kmaximv/Wi-Fi-Sensor/screenshots/Apins.png

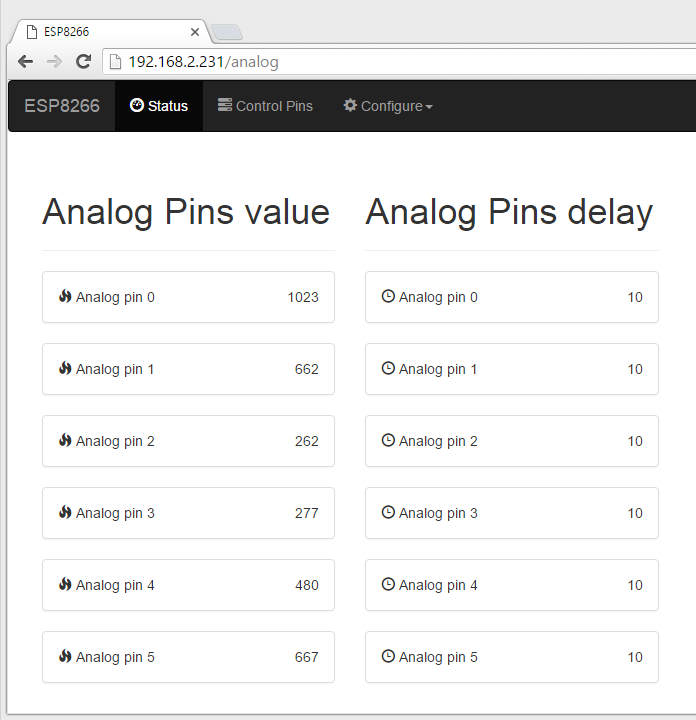
screenshots/Apins.png
