kmaximv/Wi-Fi-Sensor/screenshots/arduino-ide.png

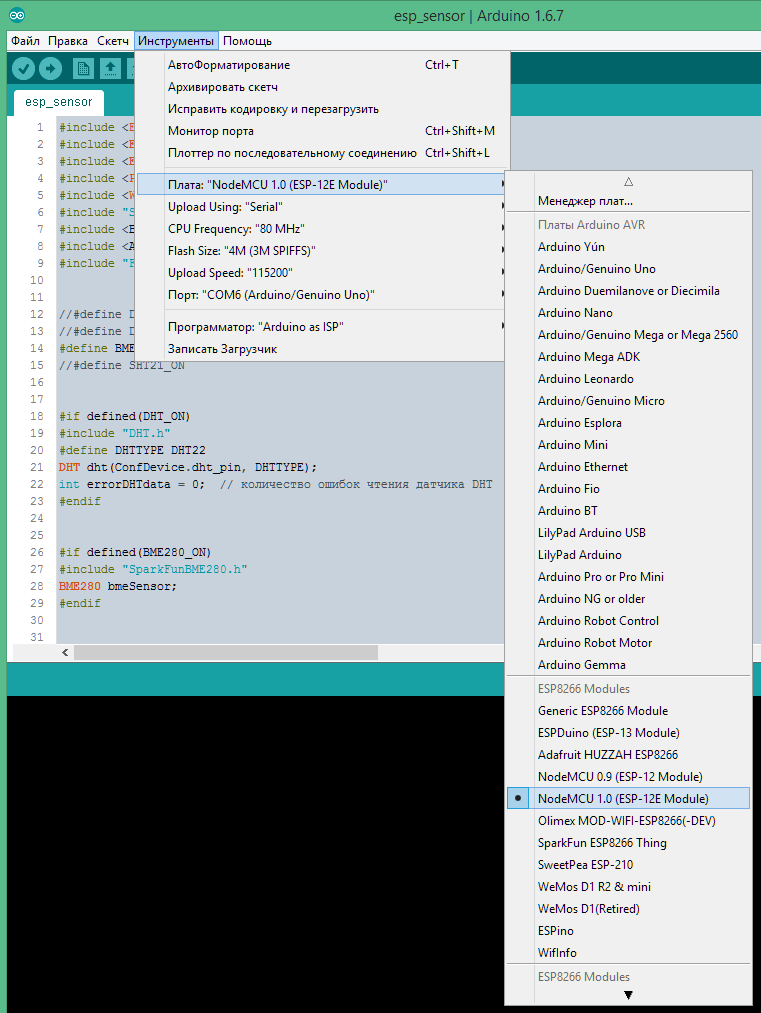
screenshots/arduino-ide.png
