kmaximv/Wi-Fi-Sensor/screenshots/HC-SR501.jpg

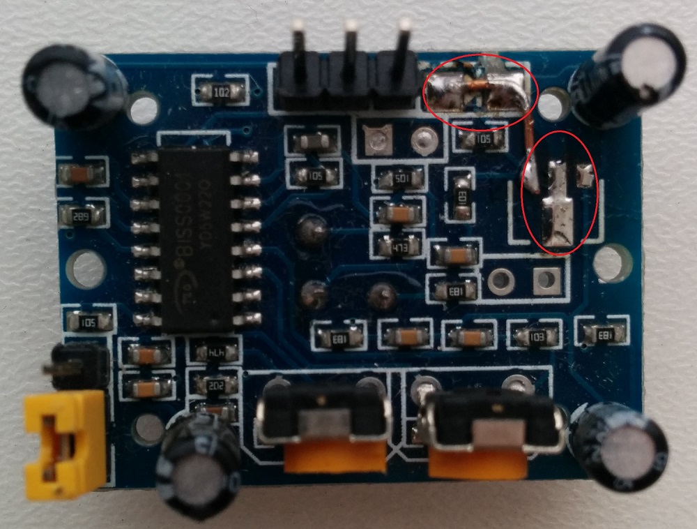
screenshots/HC-SR501.jpg
