kmaximv/Wi-Fi-Sensor/screenshots/MP1584EN.jpg

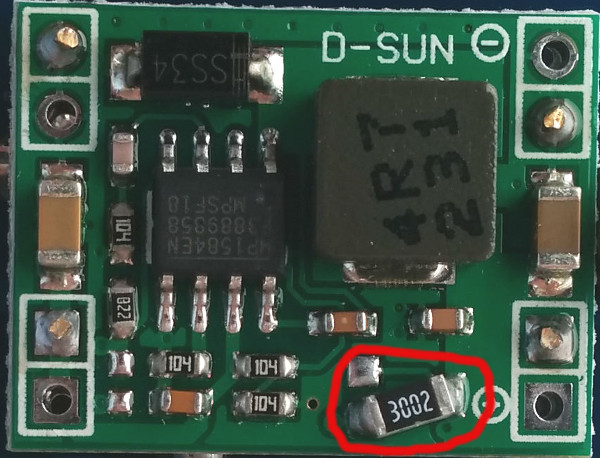
screenshots/MP1584EN.jpg
