kmaximv/Wi-Fi-Sensor/screenshots/OpenHab_graph.png

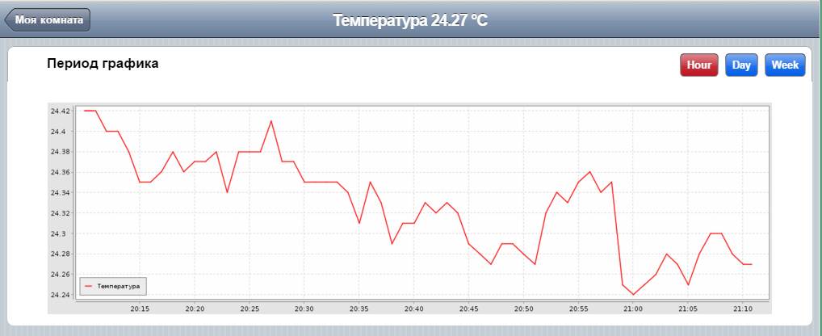
screenshots/OpenHab_graph.png
