kmaximv/Wi-Fi-Sensor/screenshots/PCB_top.png

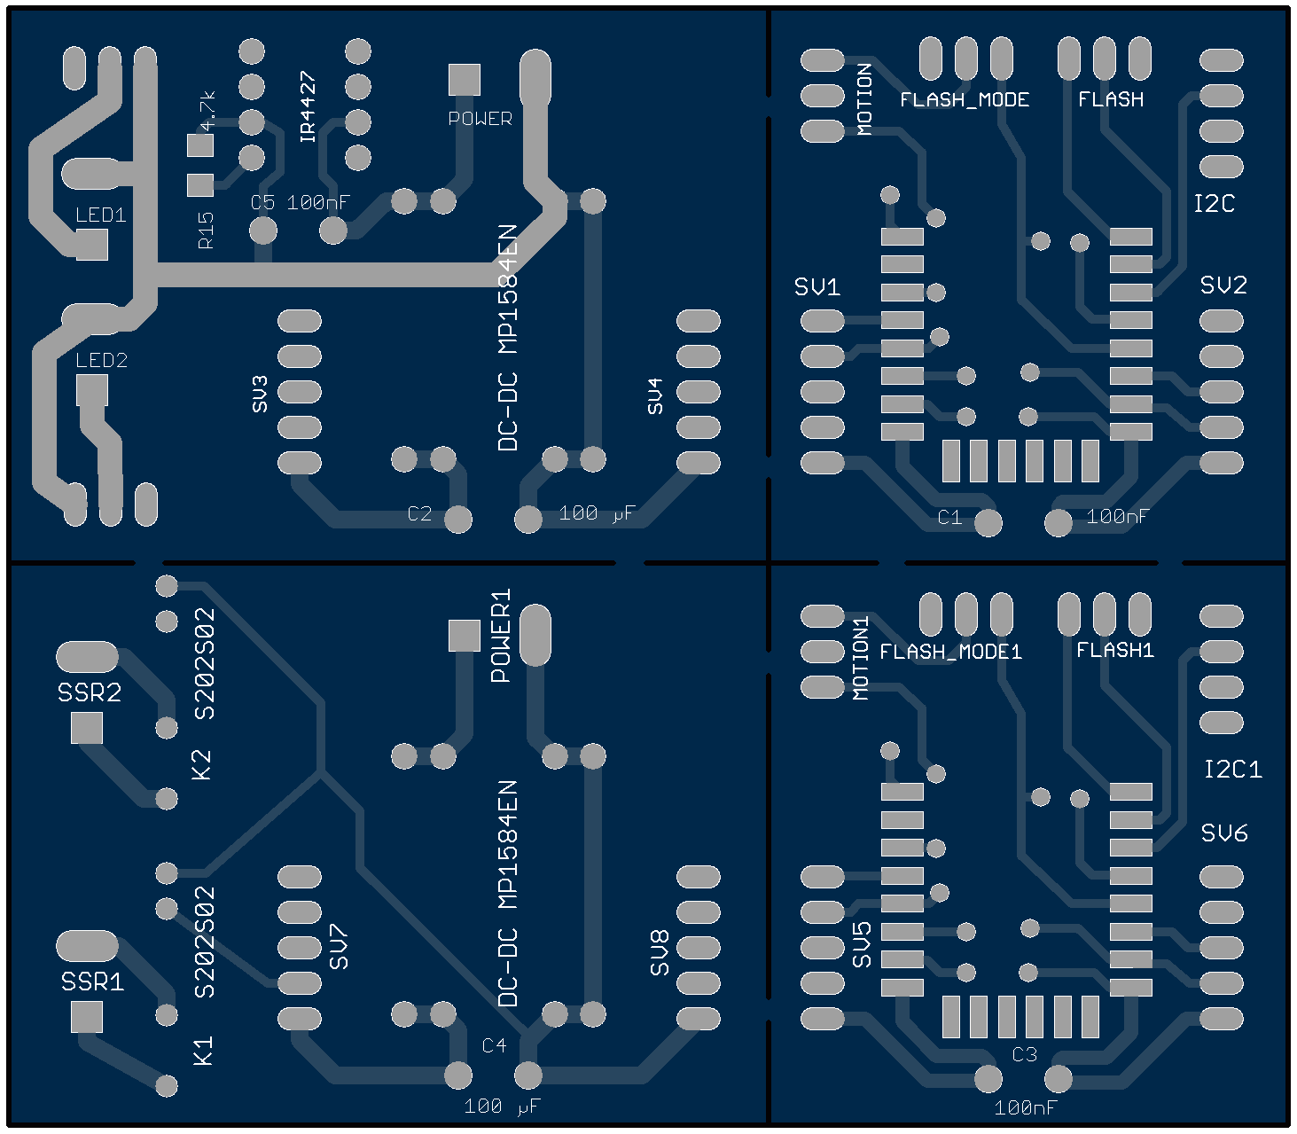
screenshots/PCB_top.png
