kmaximv/Wi-Fi-Sensor/screenshots/PZEM/CuteCom.png

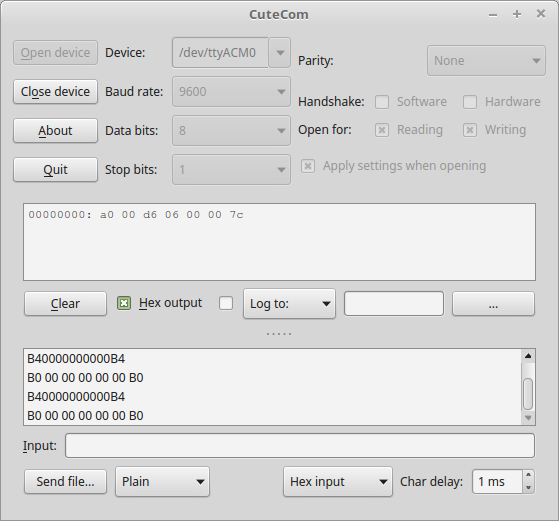
screenshots/PZEM/CuteCom.png
