kmaximv/Wi-Fi-Sensor/screenshots/PZEM/OpenHab_energy.png

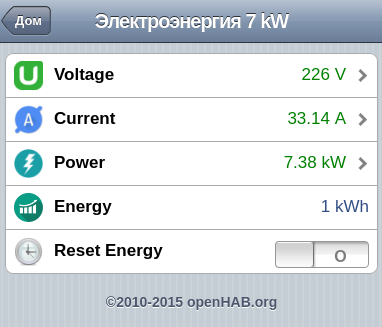
screenshots/PZEM/OpenHab_energy.png
