kmaximv/Wi-Fi-Sensor/screenshots/PZEM/pzem_status.png

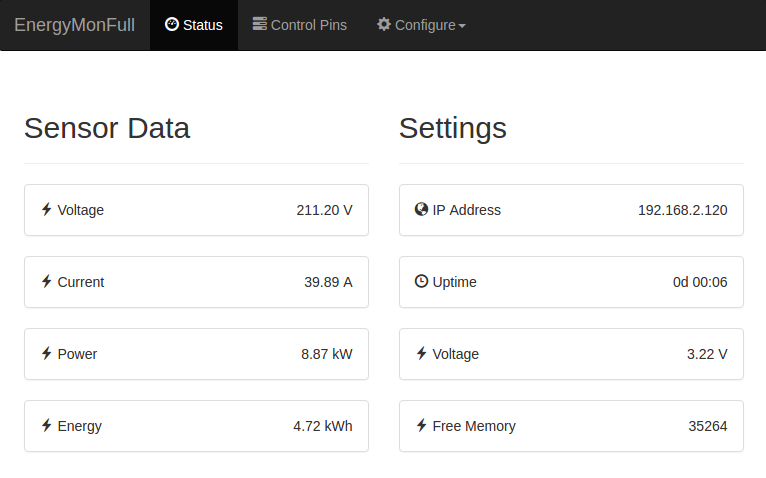
screenshots/PZEM/pzem_status.png
