kmaximv/Wi-Fi-Sensor/screenshots/Schema_LED.png

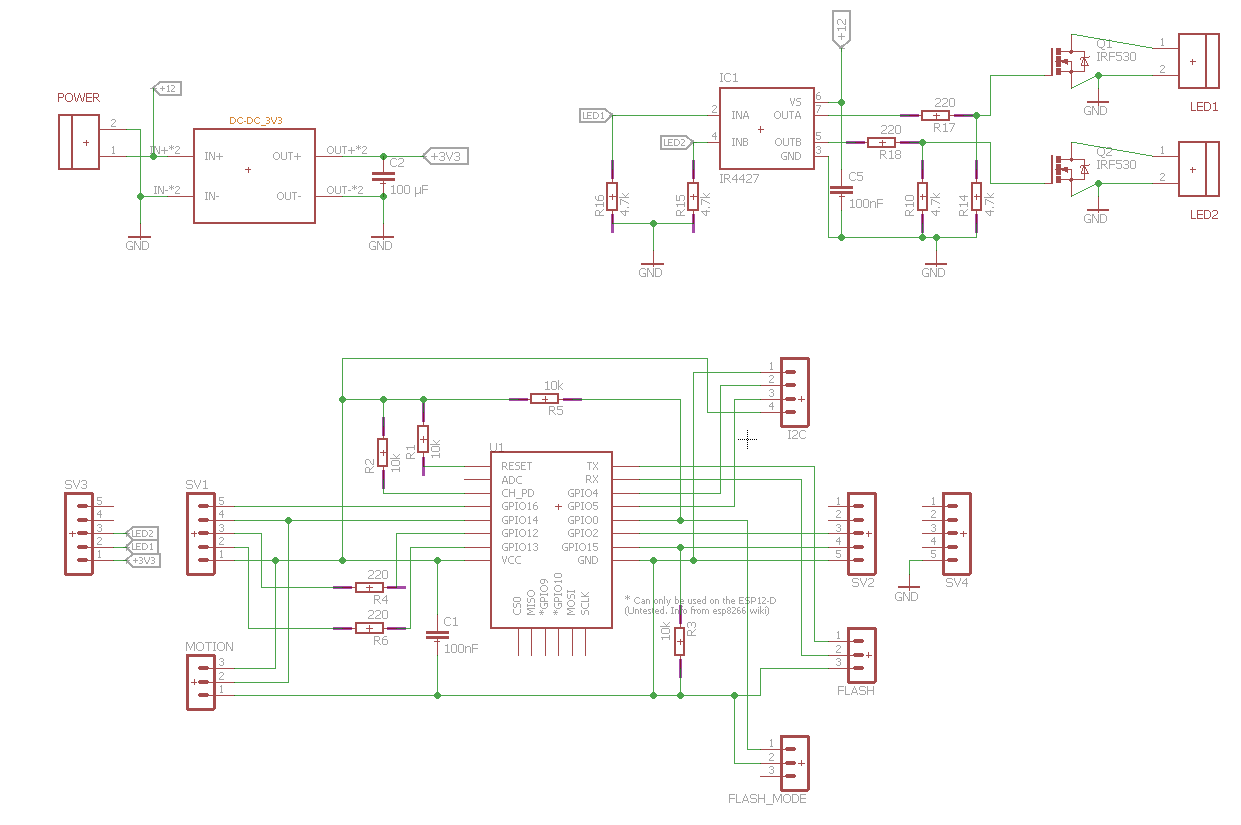
screenshots/Schema_LED.png
