kmaximv/Wi-Fi-Sensor/screenshots/Schema_SSR.png

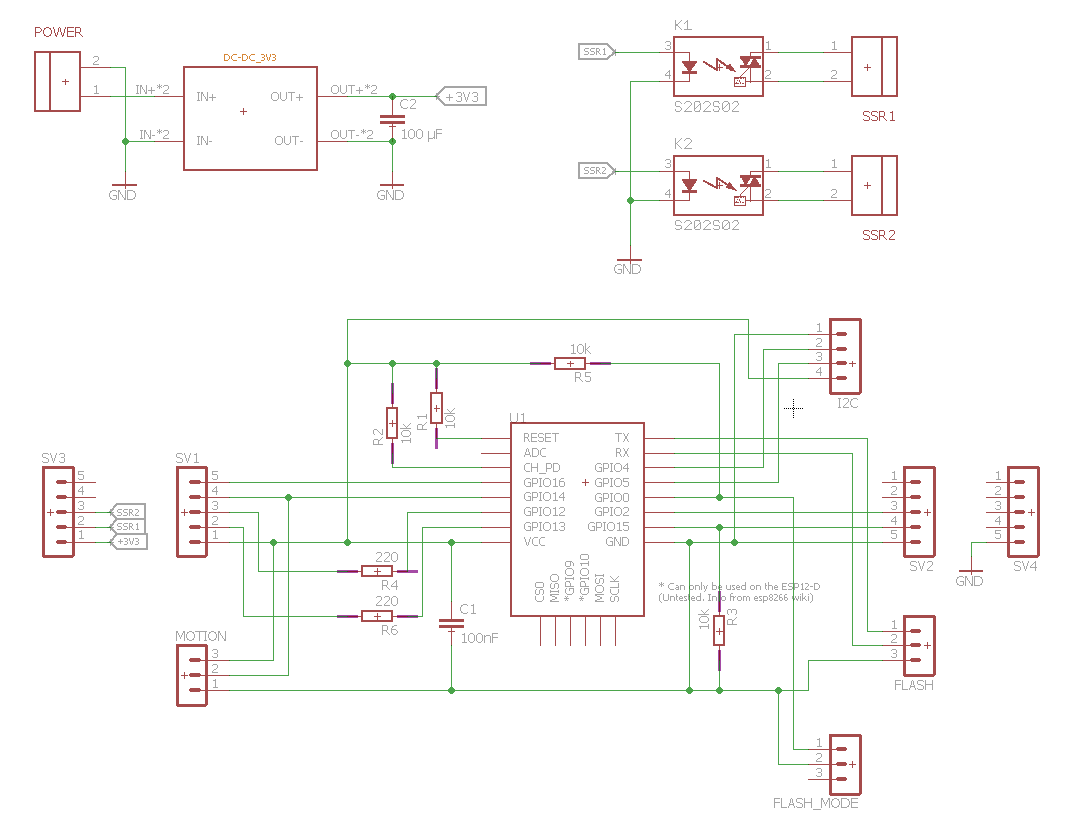
screenshots/Schema_SSR.png
