kmaximv/Wi-Fi-Sensor/screenshots/syslog.png

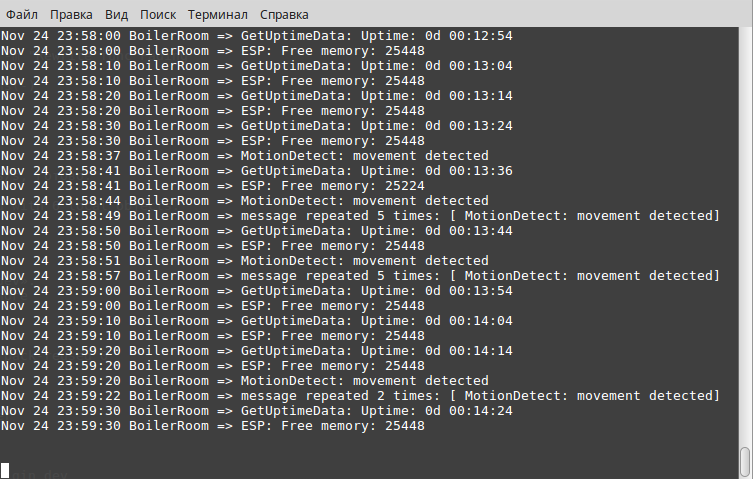
screenshots/syslog.png
