kmaximv/Wi-Fi-Sensor/screenshots/thumbs/PCB_top_th.png

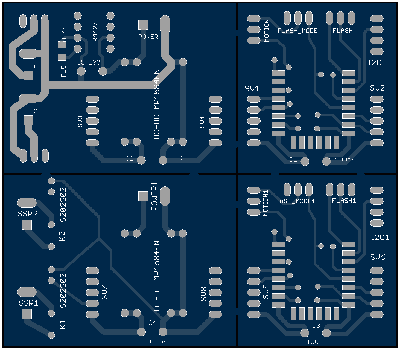
screenshots/thumbs/PCB_top_th.png
