kmaximv/Wi-Fi-Sensor/screenshots/web/console.png

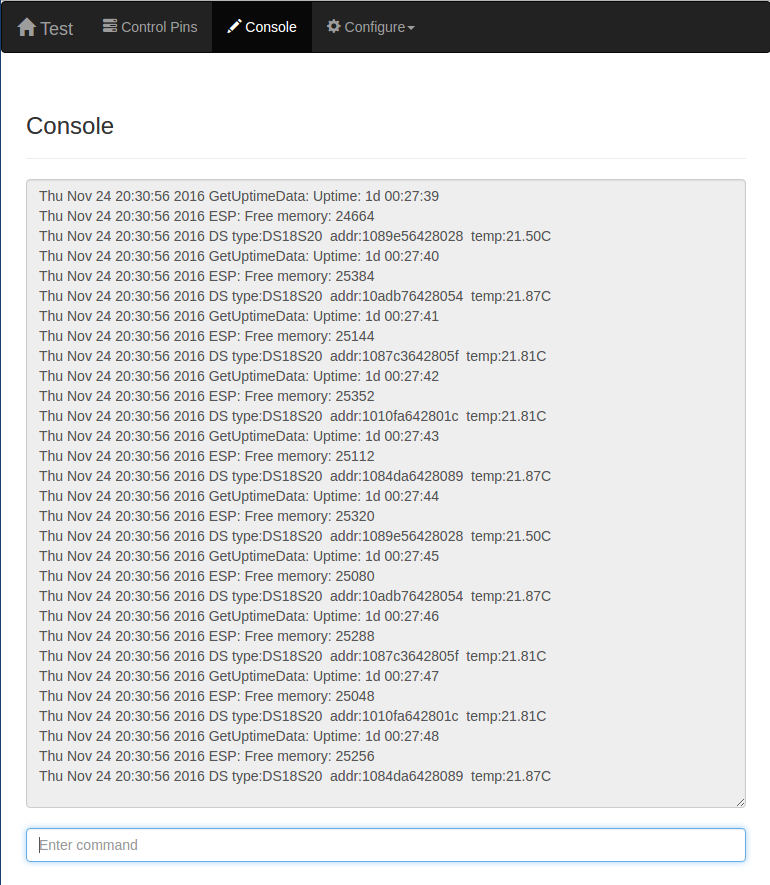
screenshots/web/console.png
