kmaximv/Wi-Fi-Sensor/screenshots/web/control.png

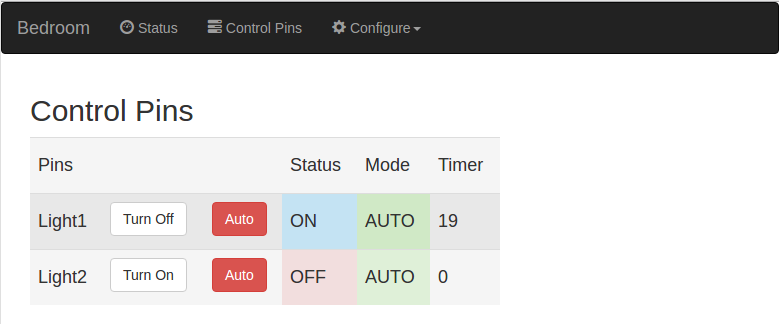
screenshots/web/control.png
