kmaximv/Wi-Fi-Sensor/screenshots/web/esp.png

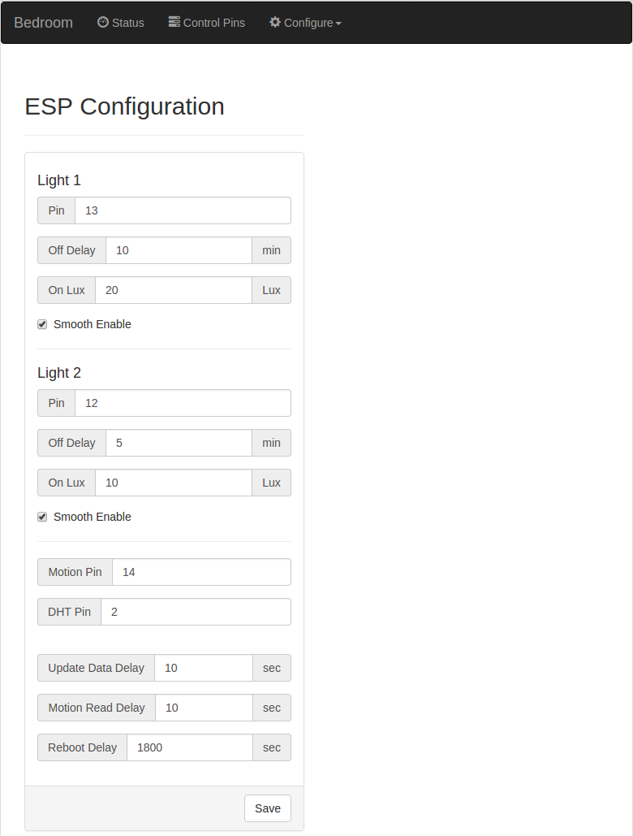
screenshots/web/esp.png
