kmaximv/Wi-Fi-Sensor/screenshots/web/logConf.png

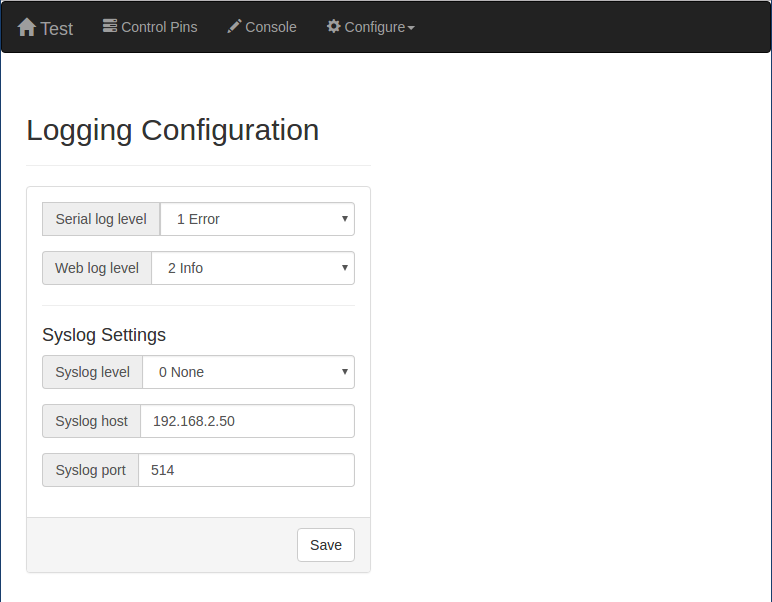
screenshots/web/logConf.png
