kmaximv/Wi-Fi-Sensor/screenshots/web/menu.png

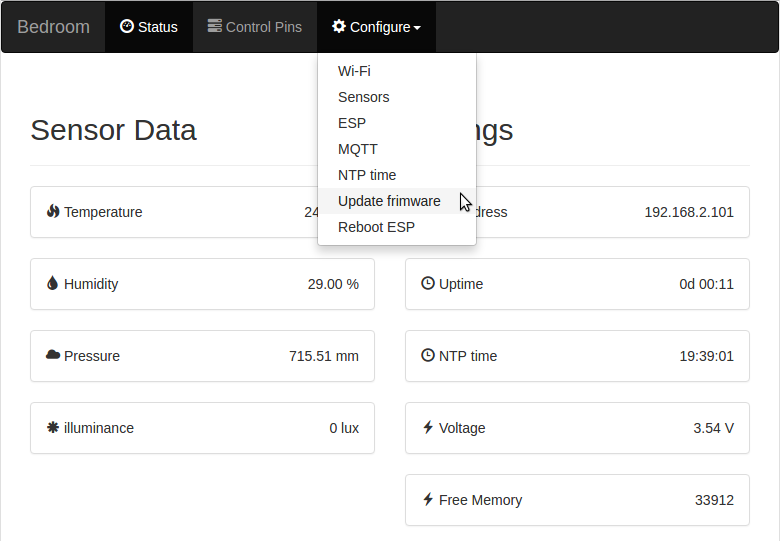
screenshots/web/menu.png
