kmaximv/Wi-Fi-Sensor/screenshots/web/mqtt.png

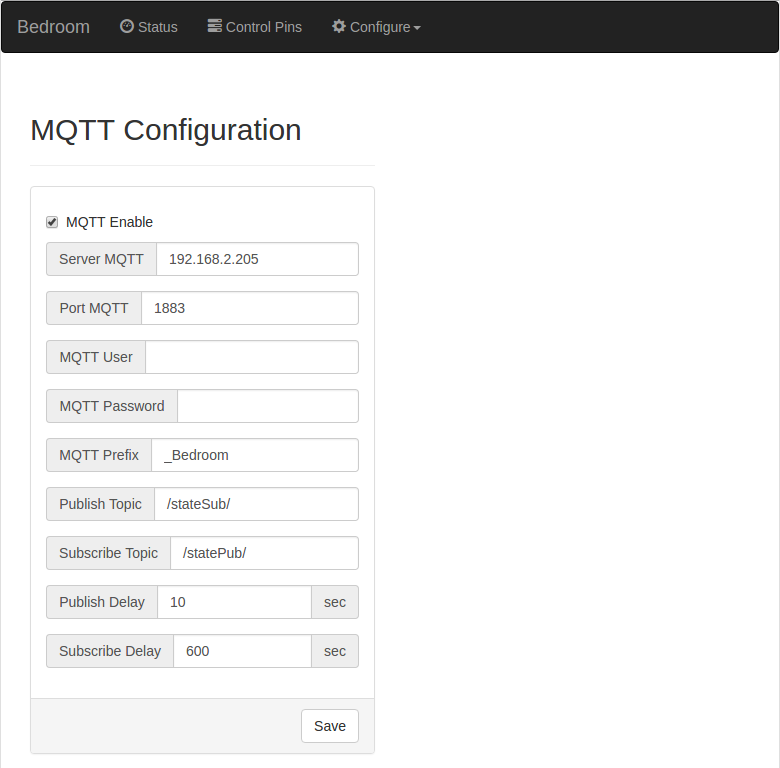
screenshots/web/mqtt.png
