kmaximv/Wi-Fi-Sensor/screenshots/web/ntp.png

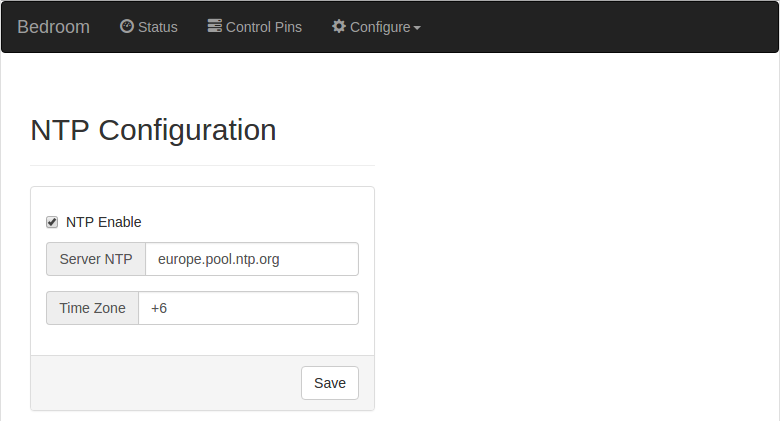
screenshots/web/ntp.png
