kmaximv/Wi-Fi-Sensor/screenshots/web/sensors.png

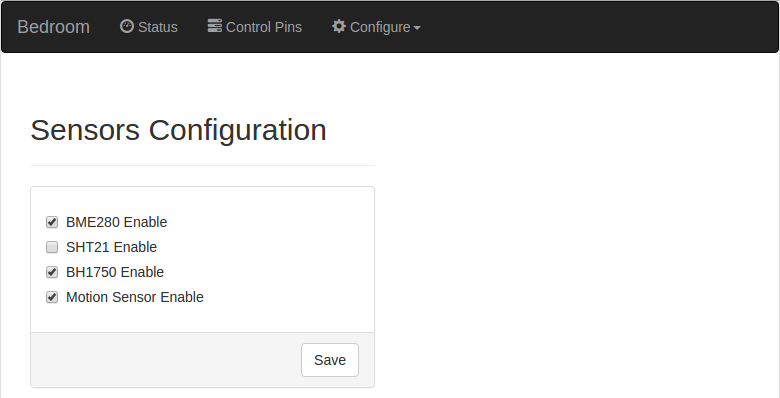
screenshots/web/sensors.png
