kmaximv/Wi-Fi-Sensor/screenshots/web/status.png

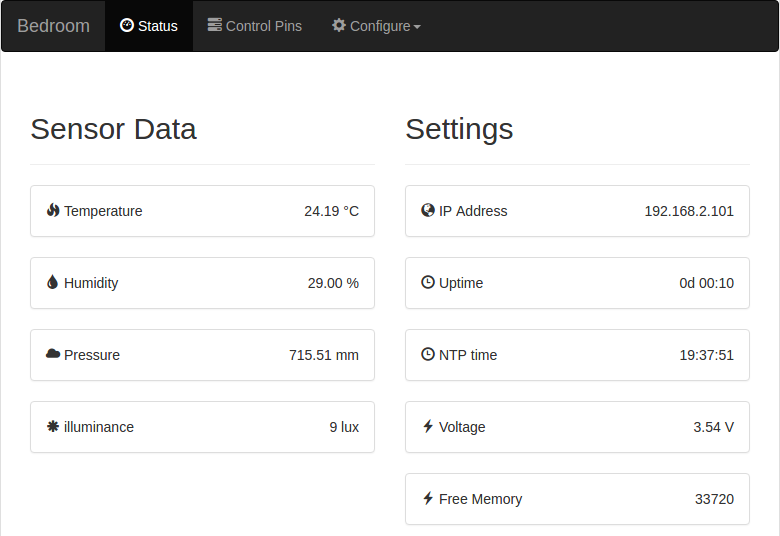
screenshots/web/status.png
