kmaximv/Wi-Fi-Sensor/screenshots/web/statusDS.png

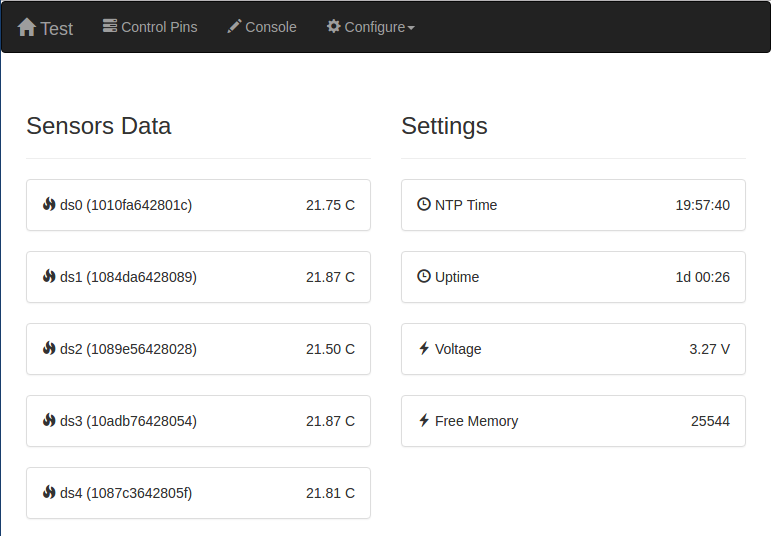
screenshots/web/statusDS.png
