kmaximv/Wi-Fi-Sensor/screenshots/web/update.png

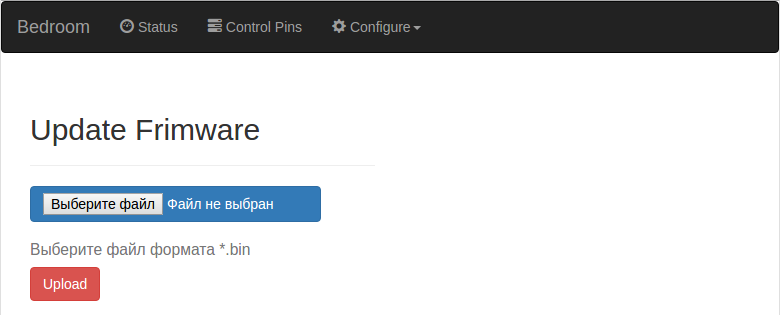
screenshots/web/update.png
