kmaximv/Wi-Fi-Sensor/screenshots/PZEM/test_sample.jpg

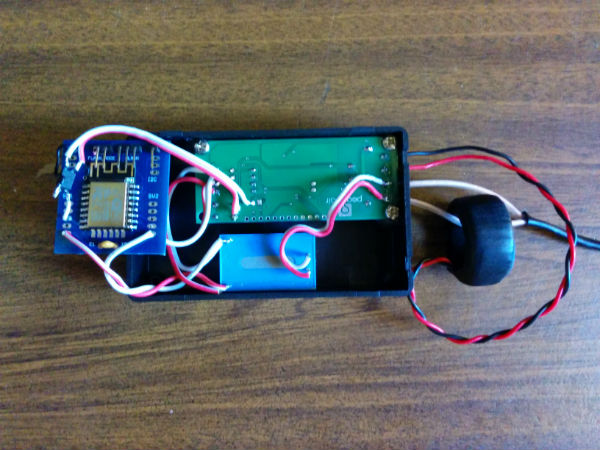
screenshots/PZEM/test_sample.jpg
