kmaximv/Wi-Fi-Sensor/esp_sensor/htmlEdit.ino

#define edit_htm_gz_len 4116
const char edit_htm_gz[] PROGMEM = {
0x1F, 0x8B, 0x08, 0x08, 0x35, 0x59, 0x0A, 0x56, 0x00, 0x03, 0x65, 0x64, 0x69, 0x74, 0x2E, 0x68, 0x74, 0x6D, 0x00, 0x9D, 0x59, 0x79, 0x77, 0xA2, 0x4A, 0x16, 0xFF, 0xFF, 0x7D, 0x0A, 0x1E, 0x3D, 0x33, 0xC2, 0xA8, 0x28, 0x98, 0xAD, 0x35, 0x24, 0xA3, 0xC6, 0x2C, 0x9D, 0x3D, 0x6A, 0xBA, 0xB3, 0xCD, 0x9C, 0x02, 0x4A, 0x40, 0xD9, 0x02, 0x18, 0x4D, 0x2C, 0xBF, 0xFB, 0xDC, 0x5B, 0x80, 0x31, 0xE9, 0x7E, 0xEF, 0xCD, 0x99, 0xCE, 0x69, 0xA8, 0xED, 0xEE, 0xBF, 0xBA, 0xB7, 0x2C, 0x76, 0x7F, 0x3F, 0xB8, 0xEC, 0x0E, 0xEE, 0xAE, 0x7A, 0x82, 0x93, 0xFA, 0xDE, 0xDE, 0x2E, 0x3E, 0x05, 0x8F, 0x04, 0xB6, 0x2E, 0xD2, 0x40, 0x84, 0x3E, 0x25, 0xD6, 0xDE, 0x6E, 0xEA, 0xA6, 0x1E, 0xDD, 0xEB, 0xF5, 0xAF, 0x84, 0x9E, 0xE5, 0xA6, 0x61, 0xBC, 0x5B, 0xCB, 0x46, 0x76, 0x93, 0xF4, 0xD5, 0xA3, 0x42, 0xFA, 0x1A, 0x51, 0x5D, 0x4C, 0xE9, 0x3C, 0xAD, 0x99, 0x49, 0x22, 0x0A, 0x3E, 0xB5, 0x5C, 0xA2, 0x8B, 0x89, 0x19, 0x53, 0x64, 0xA2, 0x98, 0xFE, 0xE2, 0xAD, 0xEA, 0x06, 0x16, 0x9D, 0x37, 0x1B, 0xF5, 0x7A, 0x2B, 0x0A, 0x13, 0x37, 0x75, 0xC3, 0xA0, 0x49, 0x8C, 0x24, 0xF4, 0xA6, 0x29, 0x6D, 0x79, 0x74, 0x94, 0x36, 0x37, 0xA3, 0x79, 0xCB, 0x08, 0x63, 0x8B, 0xC6, 0x4D, 0x35, 0x9A, 0x0B, 0x30, 0xE5, 0x5A, 0xC2, 0x97, 0x8D, 0x8D, 0x8D, 0x96, 0x41, 0xCC, 0x89, 0x1D, 0x87, 0xD3, 0xC0, 0xAA, 0x9A, 0xA1, 0x17, 0xC6, 0xCD, 0x2F, 0x87, 0x9B, 0xF8, 0xD7, 0xB2, 0xDC, 0x24, 0xF2, 0xC8, 0x6B, 0x33, 0x08, 0x03, 0x0A, 0xB4, 0xF3, 0x6A, 0xE2, 0x10, 0x2B, 0x9C, 0x35, 0xEB, 0x42, 0x5D, 0x50, 0xEB, 0xC0, 0x24, 0xB6, 0x0D, 0x22, 0xD5, 0x2B, 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
0x51, 0x95, 0xAF, 0xD8, 0x52, 0xC6, 0x89, 0xB8, 0xFE, 0xE9, 0xF5, 0x1D, 0x32, 0xA2, 0x00, 0x16, 0x02, 0xE4, 0x52, 0x5D, 0x9C, 0xA6, 0xA3, 0xEA, 0x8E, 0xB8, 0xF7, 0x2E, 0xB5, 0x96, 0x7D, 0xD1, 0xC5, 0xA2, 0x26, 0x84, 0x1C, 0xB5, 0xBA, 0xF8, 0x6E, 0x20, 0x9C, 0xAE, 0x60, 0x31, 0xEC, 0x2A, 0xC1, 0x85, 0xF1, 0x02, 0xFB, 0x48, 0x0F, 0x63, 0xEF, 0x13, 0x68, 0xE1, 0x4F, 0x83, 0x59, 0x2E, 0xFD, 0x69, 0x38, 0xDF, 0xD6, 0xA2, 0xC0, 0x4B, 0x98, 0x2E, 0x7E, 0xF8, 0x66, 0xBB, 0x5A, 0xED, 0xF2, 0xB8, 0x21, 0x41, 0xB1, 0x05, 0xAB, 0xD9, 0x48, 0x46, 0x55, 0xFA, 0x40, 0x55, 0x02, 0xAA, 0x8C, 0x00, 0x1A, 0x68, 0x09, 0x9A, 0x85, 0x9F, 0xAF, 0x7F, 0xFB, 0x2F, 0x54, 0x7A, 0x8D, 0xD0, 0xCF, 0x1E, 0x00, 0x00};
