kmaximv/Wi-Fi-Sensor/esp_sensor/MY_ESP_UART.cpp

#include "MY_ESP_UART.h"



void Espuart::SetAnalogReadCycle(int pin, int delay, String timeRank){
  String data = a;
  data += String(delimiter);
  data += String(pin);
  data += String(delimiter);
  data += String(delay);
  data += String(delimiter);
  data += timeRank;
  Send(data);
}


bool Espuart::Send(String data){
  String packet = startMarker;            // Отправляем маркер начала пакета
  packet += String(data.length());        // Отправляем длину передаваемых данных
  packet += String((char)crcCalc(data));  // Отправляем контрольную сумму данных
  packet += data;                         // Отправляем сами данные
  packet += stopMarker;                   // Отправляем маркер конца пакета
  Serial.println(packet);

  #ifdef DEBUG_ESP_UART
    Serial.println();
    Serial.print(F("Send Uart:"));  Serial.println(data);
  #endif

  if (serialEvent() &&  dataString == data){
    return true;
  }

  #ifdef DEBUG_ESP_UART
    Serial.print(F("Receive Uart:"));  Serial.println(dataString);
  #endif

  return false;
}


void Espuart::printByte(uint8_t *data) {
  Serial.println(F("printByte =================="));
  Serial.print(F("length: ")); Serial.println(dataLength);
  for (uint8_t i = 0;  i < dataLength; ++i){
    Serial.print(data[i], DEC); Serial.print(F(" "));
  }
  Serial.println();
  Serial.println(F("Done ======================="));
}


uint8_t Espuart::crc8(uint8_t crc, uint8_t data, uint8_t polynomial){
  crc ^= data;
  for (size_t i = 0; i < 8; ++i){
    crc = (crc << 1) ^ ((crc & 0x80) ? polynomial : 0);
  }
  return crc;
}


uint8_t Espuart::crc8_ccitt(uint8_t crc, uint8_t data){
  return crc8(crc, data, 0x07);
}


/* Вспомогательная функция вычисления CRC для строки */
uint8_t Espuart::crcCalc(String dataStr){

  uint8_t data[DATA_LENGTH];
  size_t length = dataStr.length();
  dataStr.getBytes(data, length + 1); // + 1 для дополнительного символа окончания строки

  #ifdef DEBUG_ESP_UART
    printByte(data);
  #endif

  uint8_t crc = 0;
  for (size_t i = 0; i < length; ++i) {
    crc = crc8_ccitt(crc, data[i]);
    #ifdef DEBUG_ESP_UART
      Serial.print(crc, DEC); Serial.print(F(" "));
    #endif
  }
  return crc;
}


bool Espuart::crcCheck(String dataStr, uint8_t crcControl) {
  uint8_t crc = crcCalc(dataStr);
  #ifdef DEBUG_ESP_UART
  Serial.print(F("CRC:        "));    Serial.println(crc);    Serial.print(F("crcControl: "));    Serial.println(crcControl);
  #endif
  if (crc == crcControl) {
    #ifdef DEBUG_ESP_UART
      Serial.println(F("CRC OK!"));
    #endif
    return true;
  } else {
    #ifdef DEBUG_ESP_UART
      Serial.println(F("CRC Error!"));
    #endif
    return false;
  }
}


void Espuart::Reset(){
  dataString = "";           // Обнуляем буфер приема данных
  startMarkerStatus = 0;     // Сброс флага маркера начала пакета
  stopMarkerStatus = 0;      // Сброс флага маркера конца пакета
  dataLength = 0;            // Сброс флага принимаемых данных
  packetAvailable = false;   // Сброс флага завершения приема пакета
  crc_byte = 0;
  for (size_t i = 0; i < PARSE_CELLS; i++) {
    parseArray[i] = "";
  }
}


void Espuart::Read(){
  while(Serial.available() && !packetAvailable) {               // Пока в буфере есть что читать и пакет не является принятым
    uint8_t bufferChar = Serial.read();                         // Читаем очередной байт из буфера
    if(startMarkerStatus < startMarker.length()) {              // Если стартовый маркер не сформирован (его длинна меньше той, которая должна быть) 
      if(startMarker[startMarkerStatus] == bufferChar) {        // Если очередной байт из буфера совпадает с очередным байтом в маркере
        startMarkerStatus++;                                    // Увеличиваем счетчик совпавших байт маркера
      } else {
        Reset();                                                // Если байты не совпали, то это не маркер. Нас нае****, расходимся. 
      }
    } else {
     // Стартовый маркер прочитан полностью
      if(dataLength <= 0) {                                     // Если длинна пакета не установлена
        dataLength = (int)bufferChar - 48;                      // Значит этот байт содержит длину пакета данных
        #ifdef DEBUG_ESP_UART
          Serial.println();   Serial.println();
          Serial.print(F("dataLength: "));  Serial.println(dataLength);
        #endif
      } else if (crc_byte <= 0) { 
        crc_byte = bufferChar;                                  // Значит этот байт содержит контрольную сумму пакета данных
        #ifdef DEBUG_ESP_UART
          Serial.print(F("crc_byte: "));  Serial.println(crc_byte);
        #endif
      } else {                                                  // Если прочитанная из буфера длинна пакета больше нуля
        if(dataLength > dataString.length()) {                  // Если длинна пакета данных меньше той, которая должна быть
          dataString += (char)bufferChar;                       // прибавляем полученный байт к строке пакета
        } else {                                                // Если с длинной пакета данных все нормально
          if(stopMarkerStatus < stopMarker.length()) {          // Если принятая длинна маркера конца пакета меньше фактической
            if(stopMarker[stopMarkerStatus] == bufferChar) {    // Если очередной байт из буфера совпадает с очередным байтом маркера
              stopMarkerStatus++;                               // Увеличиваем счетчик удачно найденных байт маркера
              if(stopMarkerStatus == stopMarker.length()) {
                #ifdef DEBUG_ESP_UART
                  Serial.println(F("Packet recieve!"));
                  Serial.println(dataString);
                #endif
                packetAvailable = true;                         // и устанавливаем флаг готовности пакета
              }
            } else {
              Reset();                                          // Иначе это не маркер, а х.з. что. Полный ресет.
            }
          }
        }
      } 
    }    
  }
}


bool Espuart::ParseCommand() {

  #ifdef CRC_ENABLE
    if (!crcCheck(dataString, crc_byte)) {
      return false;
    }
  #endif


  uint8_t z = 0;
  for ( size_t i = 0; i < dataString.length(); i++ ) {
    if (dataString[i] != delimiter ) {
      parseArray[z] += dataString[i];
    } else if (dataString[i] == delimiter ) {
      z++;
    } 
    if (z > PARSE_CELLS) {
      #ifdef DEBUG_ESP_UART
        Serial.println(F("Error Parse Command"));
      #endif
      for ( size_t i = 0; i < 3; i++ ) {
        parseArray[i] = "";
      }
      return false;
    }
  }

  #ifdef DEBUG_ESP_UART
    for ( size_t i = 0; i < 3; i++ ) {
      Serial.print(parseArray[i]);   Serial.print(F(" "));
    }
    Serial.println(F("<--"));
  #endif

  if (parseArray[0] == av) {
    #ifdef DEBUG_ESP_UART
      Serial.print(F("Analog pin: ")); Serial.print(parseArray[1]);
      Serial.print(F("   value: ")); Serial.println(parseArray[2]);
    #endif

    valueAnalogPin[parseArray[1].toInt()] = parseArray[2].toInt();
    timerAnalogPin[parseArray[1].toInt()] = millis();
  }
}


bool Espuart::serialEvent(){
  Read();                          // Вызов «читалки» принятых данных
  if(packetAvailable){             // Если после вызова «читалки» пакет полностью принят
    ParseCommand();                // Обрабатываем принятую информацию
    Reset();                       // Полный сброс протокола.
    return true;
  }
  return false;
}
