kmaximv/Wi-Fi-Sensor/esp_sensor/json_config.h

#ifndef JSON_CONFIG_H
#define JSON_CONFIG_H

#include "Arduino.h"
#include "ArduinoJson.h"
#include "FS.h"

const String ConfigFileName = "/conf.json";
//#define DEBUG_JSON_CONFIG

class JsonConf
{
  public:
    bool saveConfig();
    bool loadConfig();
    void deleteConfig();
    void printConfig();

    char module_id                    [32] = "ESP8266"            ;
    char wifi_mode                    [7]  = "STA"                ;
    char wifi_phy_mode                [4]  = "11G"                ;
    char wifi_channel                 [3]  = "12"                 ;
    char wifi_auth                    [13]  = "WPA2_PSK"          ;
    char sta_ssid                     [32] = "IoT"                ;
    char sta_pwd                      [32] = "Poiu0987"           ;
    char ap_pwd                       [32] = "Poiu0987"           ;
    char static_ip                    [16] = "192.168.2.220"      ;
    char static_gateway               [16] = "192.168.2.1"        ;
    char static_subnet                [16] = "255.255.255.0"      ;
    char ntp_server                   [32] = "europe.pool.ntp.org";
    char my_time_zone                 [4]  = "+6"                 ;
    char mqtt_server                  [32] = "192.168.2.205"      ;
    char mqtt_port                    [6]  = "1883"               ;
    char mqtt_user                    [32] = "none"               ;
    char mqtt_pwd                     [32] = "none"               ;
    char mqtt_name                    [32] = "_BedM"              ;
    char publish_topic                [32] = "/stateSub/"         ;
    char subscribe_topic              [32] = "/statePub/"         ;
    char command_pub_topic            [32] = "/commandPub/"       ;
    char light_pin                    [3]  = "13"                 ;
    char lightoff_delay               [32] = "5"                  ;
    char lighton_lux                  [6]  = "10"                 ; // Значение в люксах, ниже которого будет включаться нагрузка
    char light_smooth                 [2]  = "0"                  ;
    char light2_pin                   [3]  = "12"                 ;
    char light2off_delay              [32] = "5"                  ;
    char light2on_lux                 [6]  = "10"                 ; // Значение в люксах, ниже которого будет включаться нагрузка
    char light2_smooth                [2]  = "0"                  ;
    char reset_pin                    [3]  = "2"                  ;
    char motion_pin                   [3]  = "14"                 ;
    char dht_pin                      [3]  = "2"                  ;
    char encoder_pin_a                [3]  = "4"                  ;
    char encoder_pin_b                [3]  = "5"                  ;
    char get_data_delay               [32] = "10"                 ;
    char publish_delay                [32] = "10"                 ;
    char subscribe_delay              [32] = "60"                 ;
    char motion_read_delay            [32] = "10"                 ;
    char reboot_delay                 [32] = "1800"               ;

    char sys_log_host                 [33] = "192.168.2.50"       ;
    char sys_log_port                 [6]  = "514"                ;
    char sys_log_level                [2]  = "0"                  ;
    char serial_log_level             [2]  = "0"                  ;
    char web_log_level                [2]  = "0"                  ;

    char boiler_get_temperature       [32] = "Temp_BedM"          ; //За какой температурой будет следить котел (подписываемся на mqtt топик)
    char boiler_set_temperature       [6]  = "25"                 ; //Температура, которую будем поддерживать в комнате

    char uart_delay_analog_pin0       [32] = "none"               ;
    char uart_delay_analog_pin1       [32] = "none"               ;
    char uart_delay_analog_pin2       [32] = "none"               ;
    char uart_delay_analog_pin3       [32] = "none"               ;
    char uart_delay_analog_pin4       [32] = "none"               ;
    char uart_delay_analog_pin5       [32] = "none"               ;
    char green_light_on               [6]  = "8:00"               ;
    char green_light_off              [6]  = "22:00"              ;
    char green_light_pin              [3]  = "12"                 ;
    char green_humidity_threshold_up  [5]  = "800"                ;
    char green_humidity_threshold_down[5]  = "250"                ;
    char green_humidity_sensor_pin    [3]  = "20"                 ;
    char green_pump_pin               [3]  = "33"                 ;

    char static_ip_enable             [2]  = "0"                  ;
    char ntp_enable                   [2]  = "0"                  ;
    char mqtt_enable                  [2]  = "0"                  ;
    char mqtt_auth_enable             [2]  = "0"                  ;
    char dht_enable                   [2]  = "0"                  ;
    char bme280_enable                [2]  = "0"                  ;
    char sht21_enable                 [2]  = "0"                  ;
    char bh1750_enable                [2]  = "0"                  ;
    char motion_sensor_enable         [2]  = "0"                  ;
    char pzem_enable                  [2]  = "0"                  ;
    char mhz19_enable                 [2]  = "0"                  ;
    char ds18x20_enable               [2]  = "0"                  ;
    char boiler_enable                [2]  = "0"                  ;


  private:
};

#endif
